neotwig/Origin/Enclosure Design/3.2 inch display/front white.stl

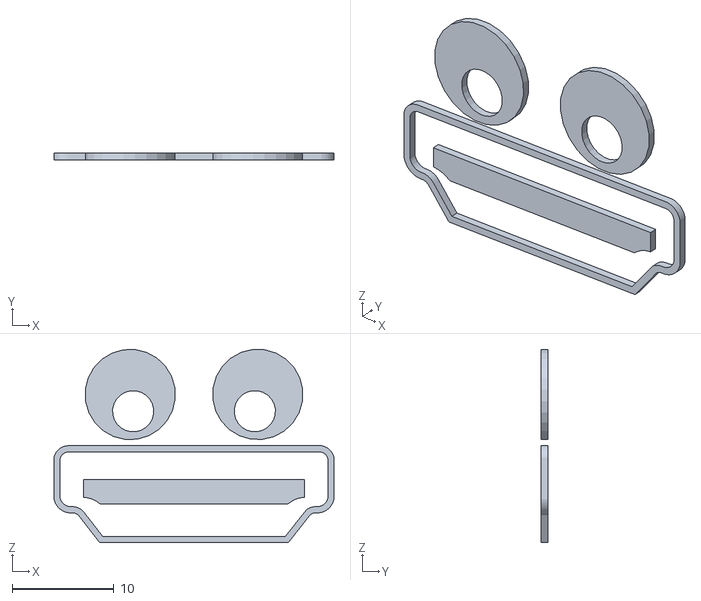
[picture p15: CAD file, 2021-12-31]
Enclosure Design/3.2 inch display/front white.stl
27.5 x 0.65 x 19.0
