neotwig/Origin/Enclosure Design/7.0 inch display/back panel white.stl

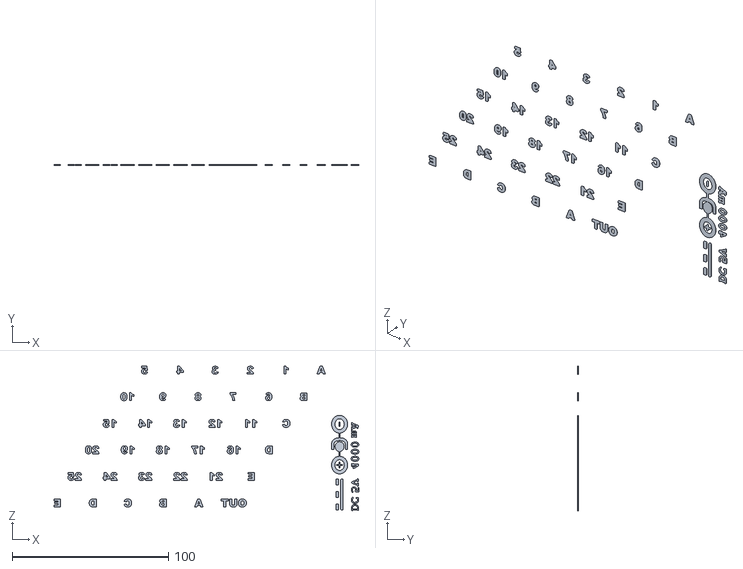
[picture p16: CAD file, 2021-12-31]
Enclosure Design/7.0 inch display/back panel white.stl
195.0 x 0.65 x 92.5
