neotwig/Origin/Enclosure Design/3.2 inch display/top panel.stl

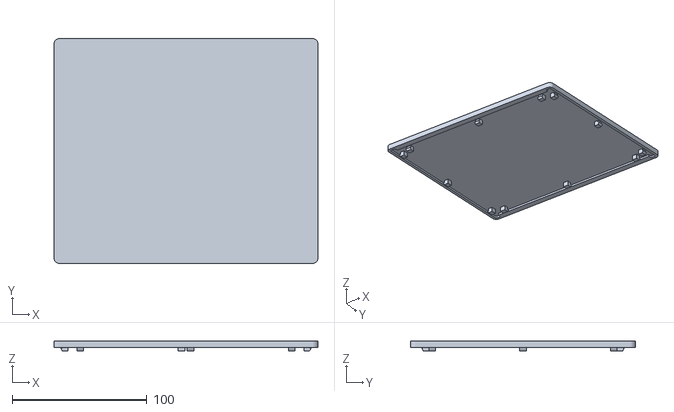
[picture p17: CAD file, 2021-12-31]
Enclosure Design/3.2 inch display/top panel.stl
195.8 x 166.7 x 7.50
