neotwig/Origin/Enclosure Design/7.0 inch display/front panel black.stl

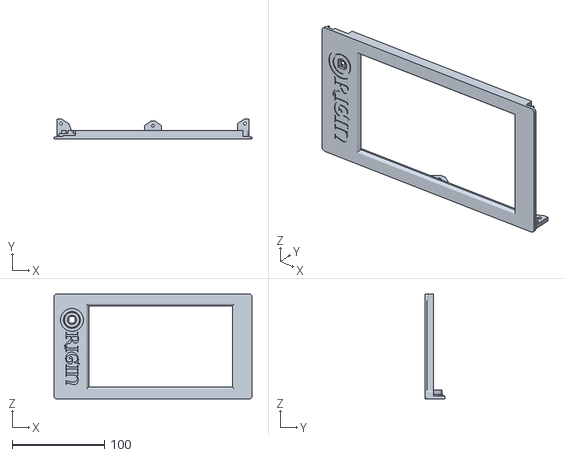
[picture p18: CAD file, 2021-12-31]
Enclosure Design/7.0 inch display/front panel black.stl
215.0 x 22.3 x 114.0
