neotwig/Origin/Enclosure Design/3.2 inch display/right panel.stl

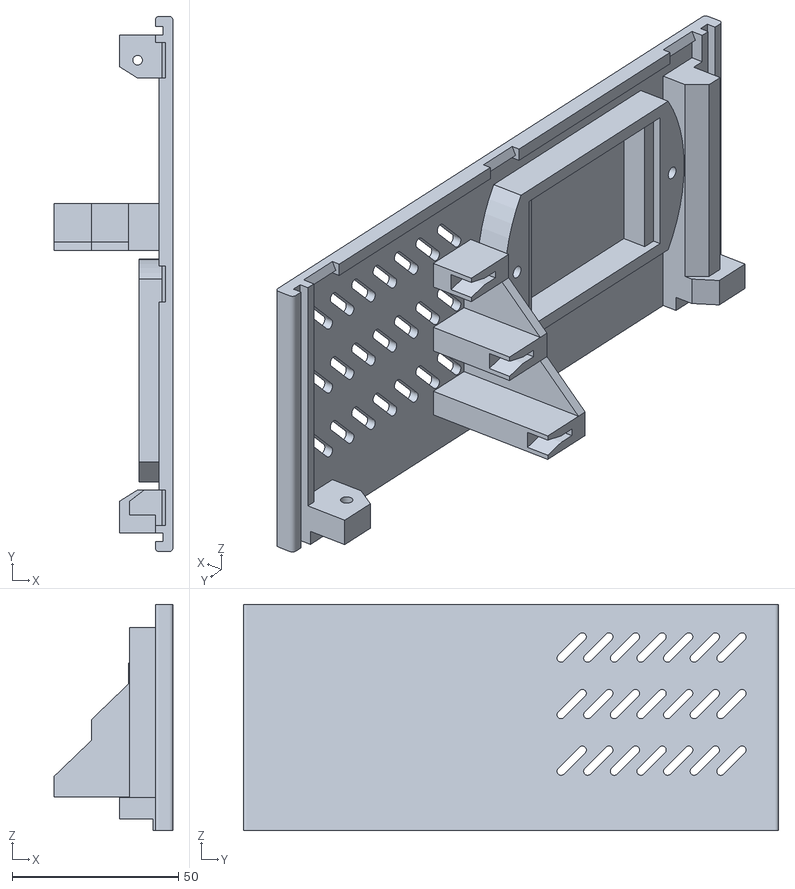
[picture p19: CAD file, 2021-12-31]
Enclosure Design/3.2 inch display/right panel.stl
35.7 x 160.8 x 68.0
