neotwig/Origin/Enclosure Design/7.0 inch display/right panel.stl

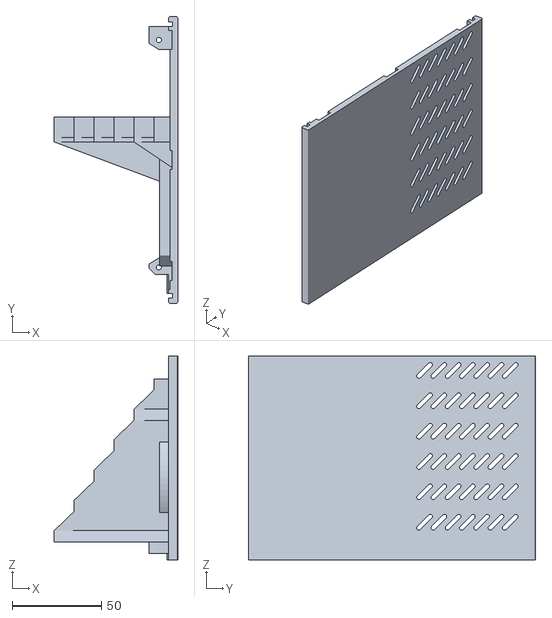
[picture p20: CAD file, 2021-12-31]
Enclosure Design/7.0 inch display/right panel.stl
69.2 x 160.8 x 114.0
