neotwig/Origin/Enclosure Design/3.2 inch display/front black.stl

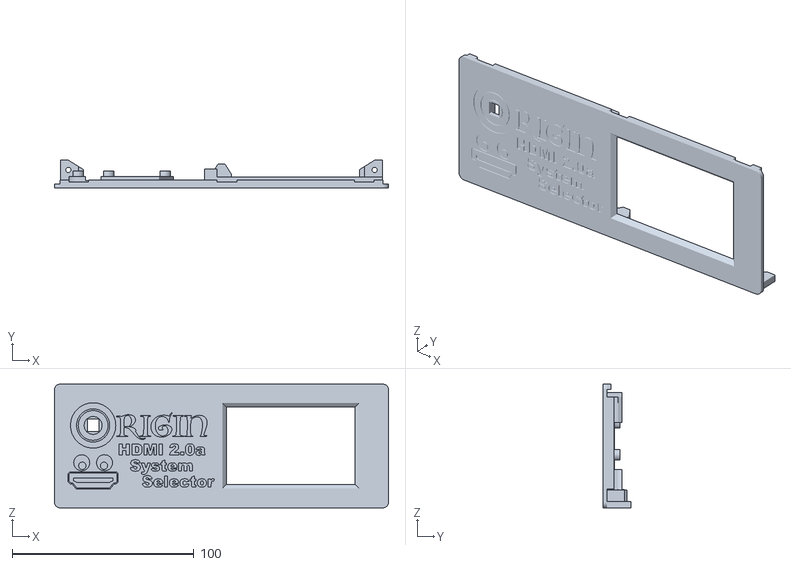
[picture p21: CAD file, 2021-12-31]
Enclosure Design/3.2 inch display/front black.stl
183.7 x 15.3 x 68.0
