neotwig/Origin/Enclosure Design/3.2 inch display/back 1 swx white.stl

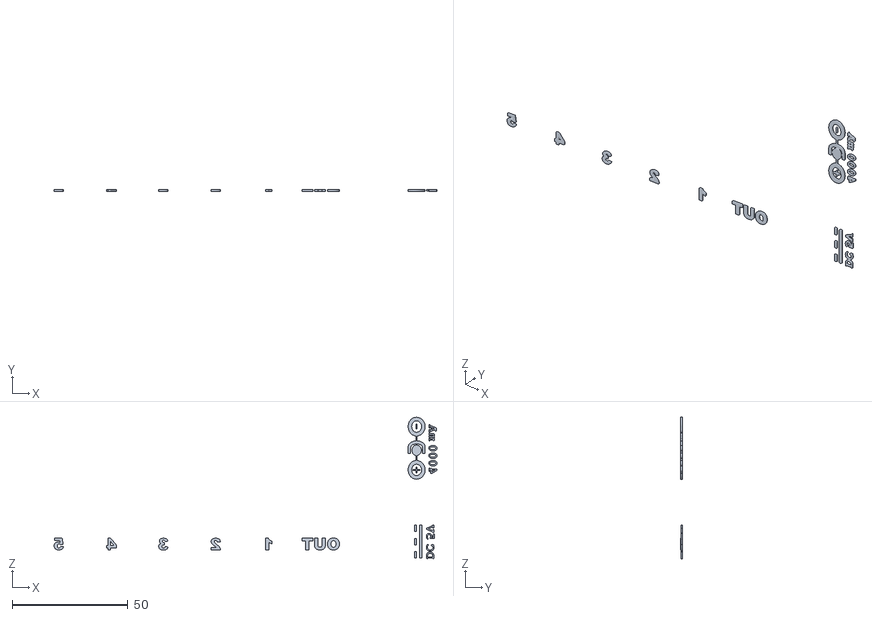
[picture p22: CAD file, 2021-12-31]
Enclosure Design/3.2 inch display/back 1 swx white.stl
165.1 x 0.653 x 61.1
