neotwig/Origin/Enclosure Design/3.2 inch display/front green.stl

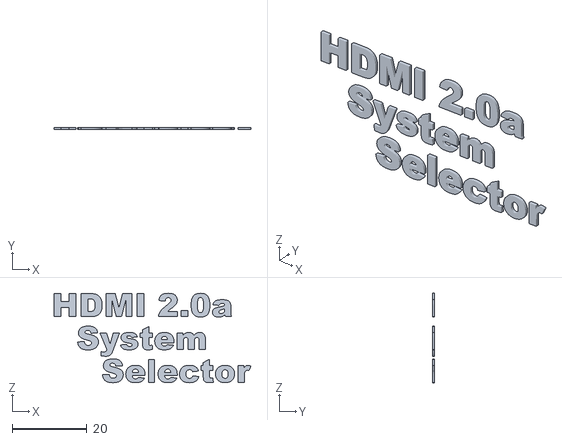
[picture p23: CAD file, 2021-12-31]
Enclosure Design/3.2 inch display/front green.stl
52.6 x 0.65 x 23.9
