neotwig/Origin/Enclosure Design/3.2 inch display/front red.stl

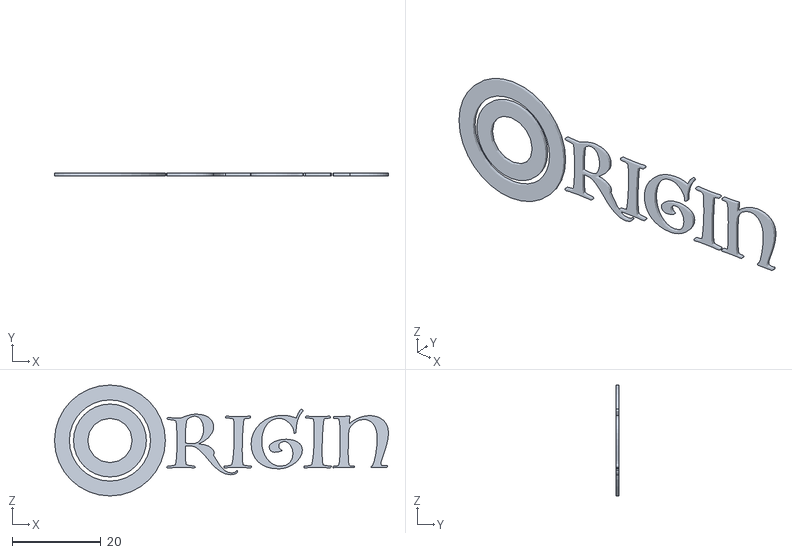
[picture p24: CAD file, 2021-12-31]
Enclosure Design/3.2 inch display/front red.stl
75.2 x 0.65 x 25.0
