neotwig/Origin/Enclosure Design/3.2 inch display/left panel.stl

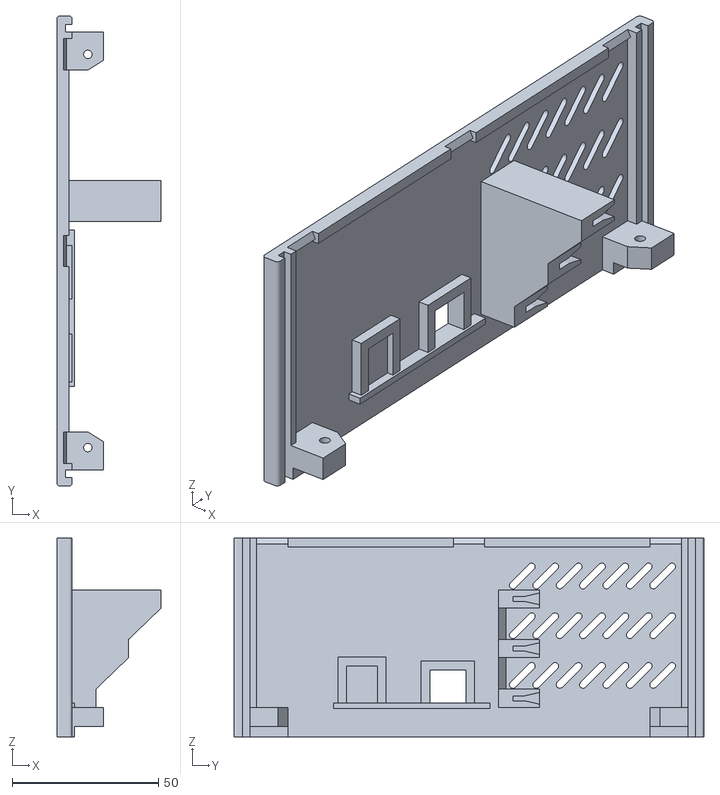
[picture p25: CAD file, 2021-12-31]
Enclosure Design/3.2 inch display/left panel.stl
35.7 x 160.7 x 68.0
